ElvisTang123/Sumo_Bot/CAD Files/angledMotHolder.SLDPRT

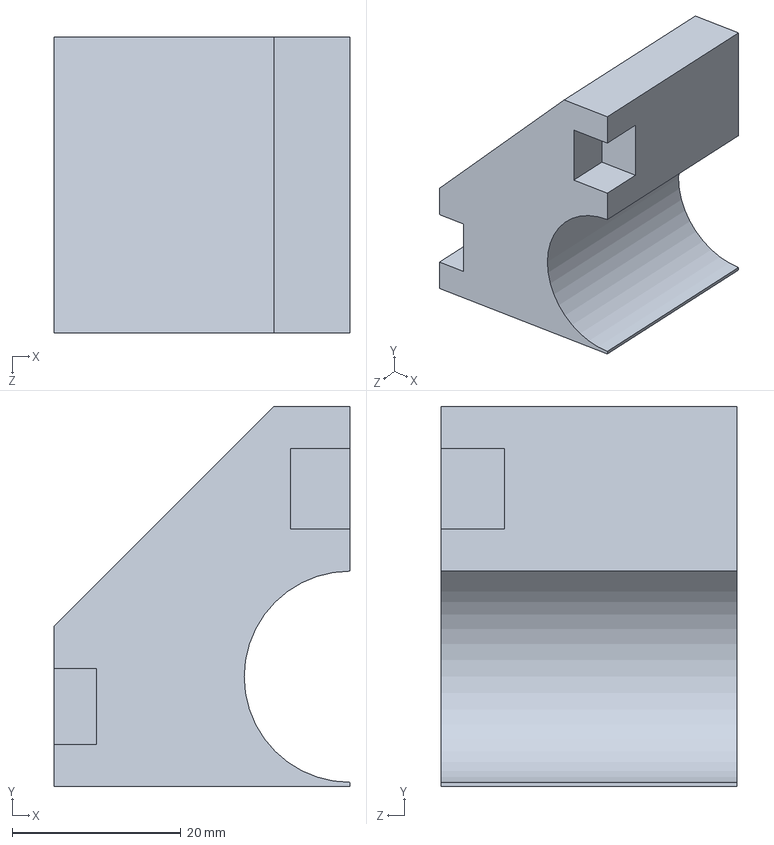
[picture p22: CAD file, 2022-08-17]
CAD Files/angledMotHolder.SLDPRT
35.0 x 45.0 x 35.0 mm
