ElvisTang123/Sumo_Bot/CAD Files/topplate.SLDPRT

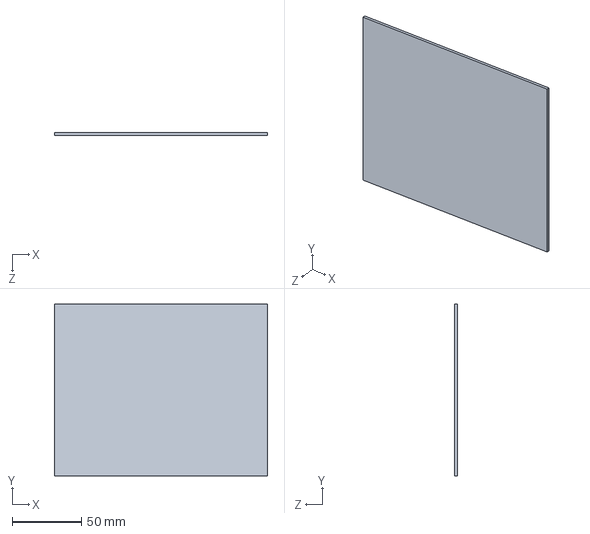
[picture p23: CAD file, 2022-08-17]
CAD Files/topplate.SLDPRT
154.0 x 124.0 x 2.00 mm
