ElvisTang123/Sumo_Bot/CAD Files/Hinge Rod.SLDPRT

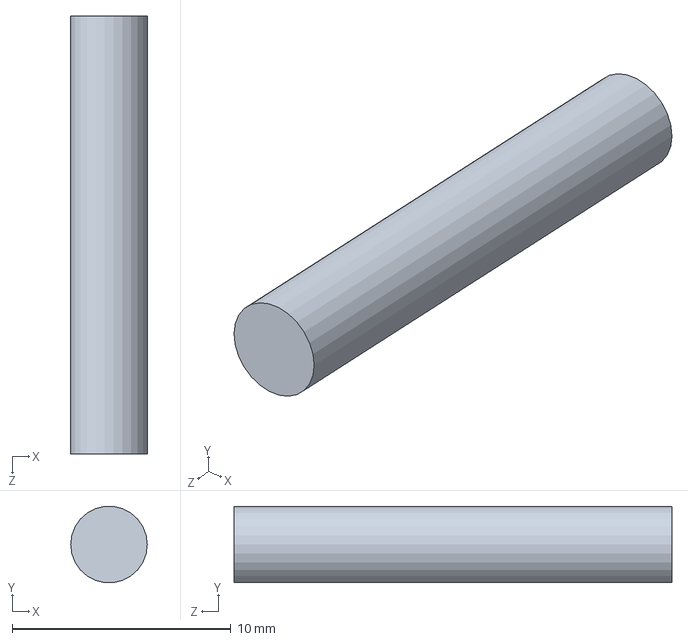
[picture p24: CAD file, 2022-08-17]
CAD Files/Hinge Rod.SLDPRT
3.50 x 3.47 x 20.0 mm
