ElvisTang123/Sumo_Bot/CAD Files/SMD Capacitor, MPU-9255.SLDPRT

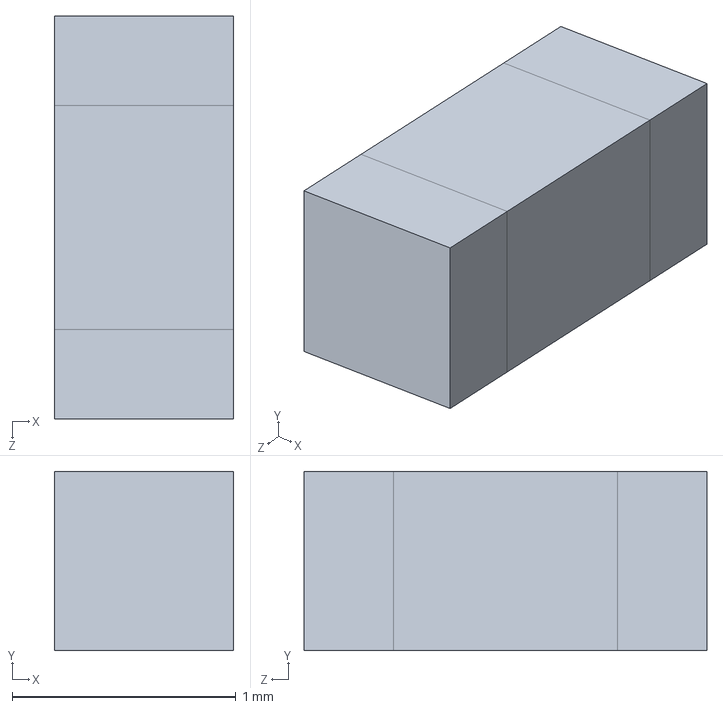
[picture p25: CAD file, 2022-08-17]
CAD Files/SMD Capacitor, MPU-9255.SLDPRT
0.8 x 0.8 x 1.80 mm
