ElvisTang123/Sumo_Bot/CAD Files/PCB, MPU-9255.SLDPRT

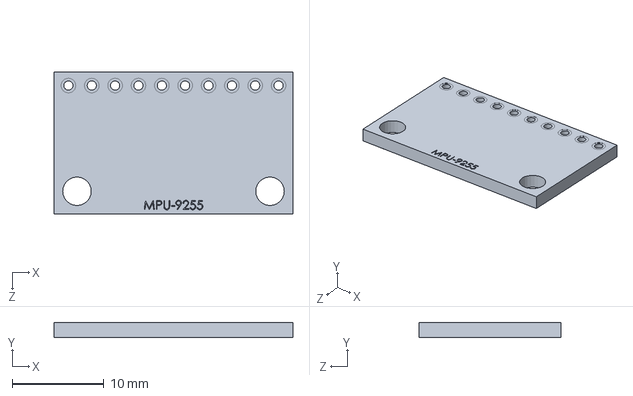
[picture p26: CAD file, 2022-08-17]
CAD Files/PCB, MPU-9255.SLDPRT
26.0 x 1.60 x 15.5 mm
