ElvisTang123/Sumo_Bot/CAD Files/SideWall.SLDPRT

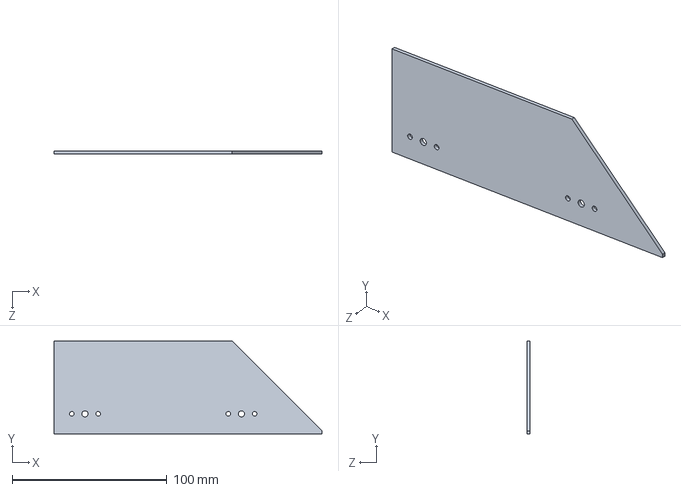
[picture p27: CAD file, 2022-08-17]
CAD Files/SideWall.SLDPRT
173.0 x 60.0 x 2.00 mm
