ElvisTang123/Sumo_Bot/CAD Files/SMD Resistor, 10kΩ, MPU-9255.SLDPRT

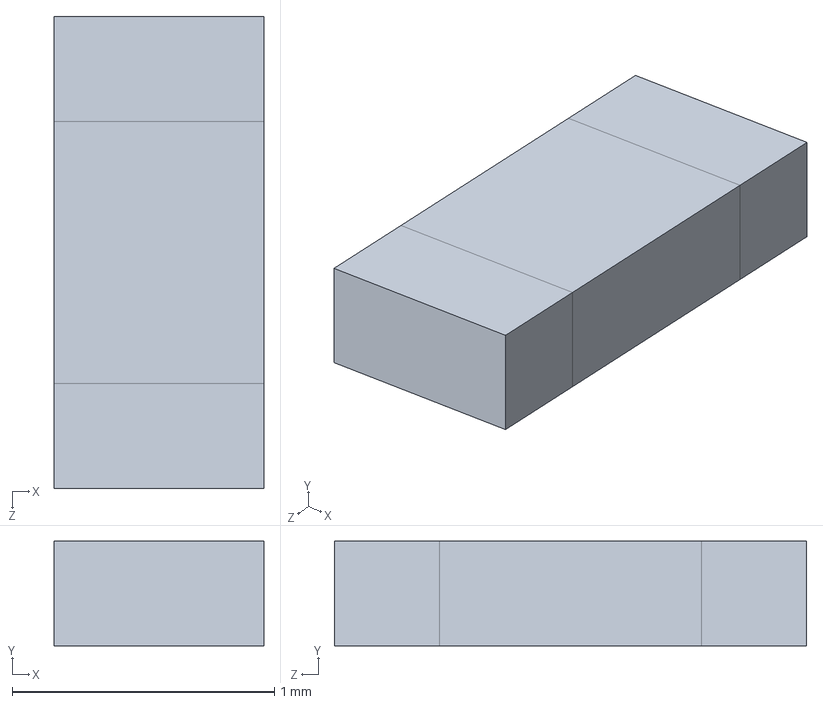
[picture p28: CAD file, 2022-08-17]
CAD Files/SMD Resistor, 10kΩ, MPU-9255.SLDPRT
0.8 x 0.4 x 1.80 mm
