ElvisTang123/Sumo_Bot/CAD Files/backplate.SLDPRT

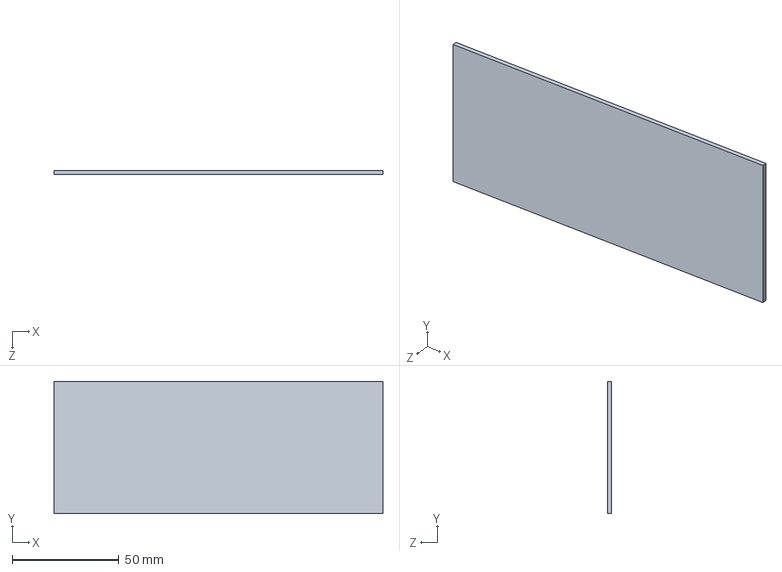
[picture p29: CAD file, 2022-08-17]
CAD Files/backplate.SLDPRT
154.0 x 62.0 x 2.00 mm
