ElvisTang123/Sumo_Bot/CAD Files/reciever.SLDPRT

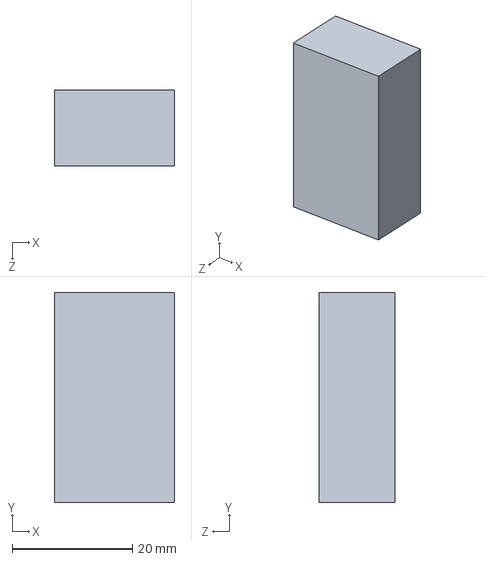
[picture p30: CAD file, 2022-08-17]
CAD Files/reciever.SLDPRT
20.0 x 35.0 x 12.7 mm
