ElvisTang123/Sumo_Bot/CAD Files/bot-angle.SLDPRT

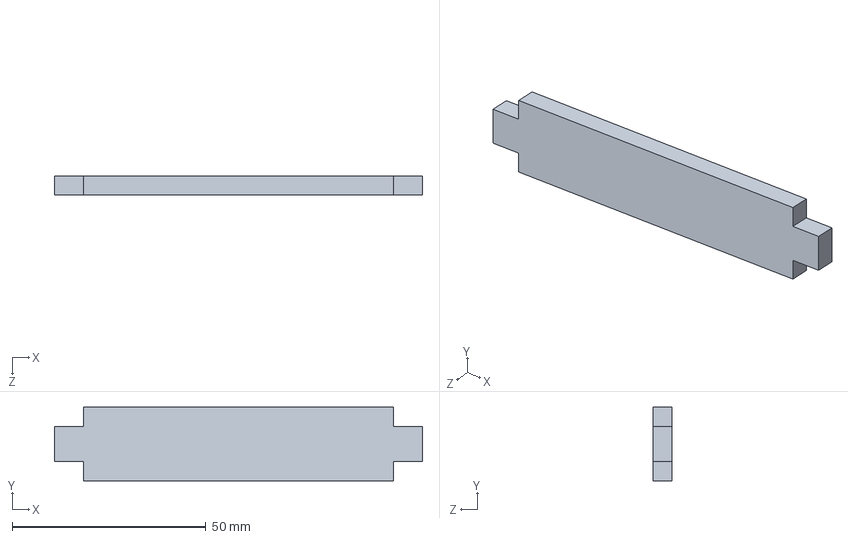
[picture p31: CAD file, 2022-08-17]
CAD Files/bot-angle.SLDPRT
95.0 x 19.0 x 5.00 mm
