ElvisTang123/Sumo_Bot/CAD Files/bottomPlate.SLDPRT

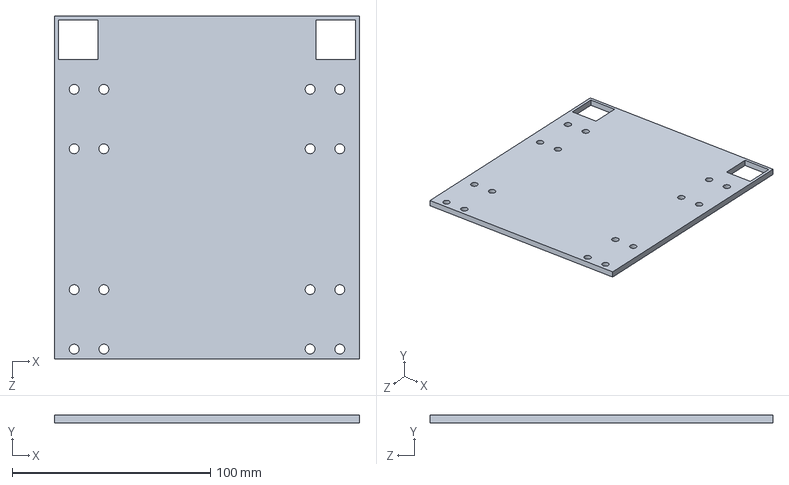
[picture p32: CAD file, 2022-08-17]
CAD Files/bottomPlate.SLDPRT
154.0 x 4.00 x 173.0 mm
