ElvisTang123/Sumo_Bot/CAD Files/vl53l0x_PCB.SLDPRT

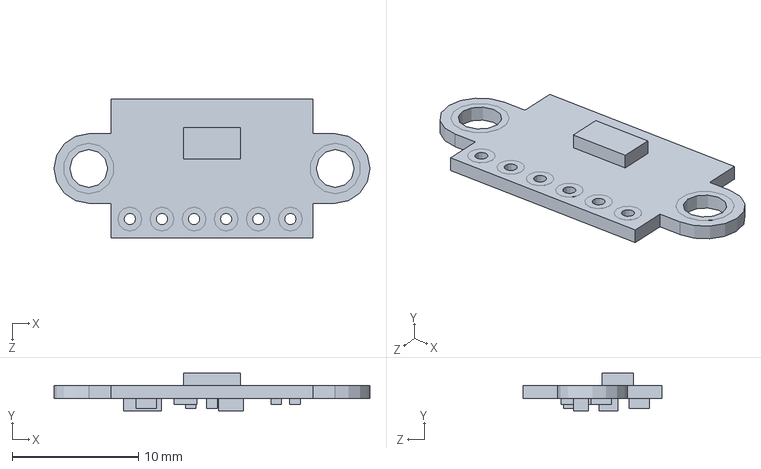
[picture p33: CAD file, 2022-08-17]
CAD Files/vl53l0x_PCB.SLDPRT
25.0 x 3.00 x 11.0 mm
