ElvisTang123/Sumo_Bot/CAD Files/Hinge2.SLDPRT

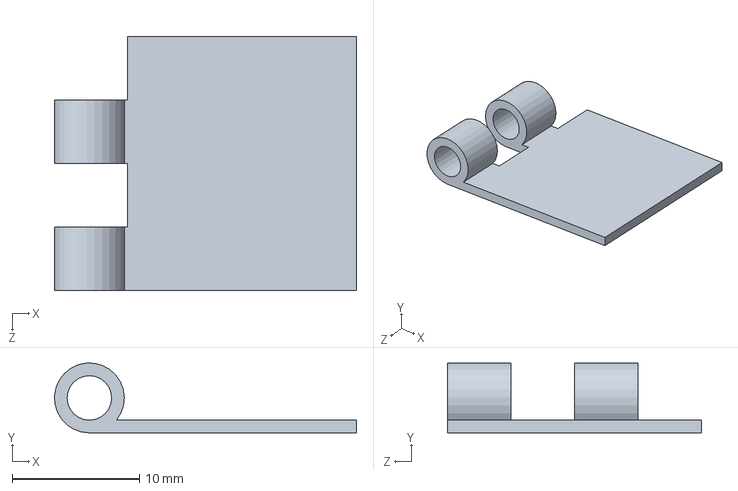
[picture p34: CAD file, 2022-08-17]
CAD Files/Hinge2.SLDPRT
23.7 x 5.49 x 20.0 mm
