ElvisTang123/Sumo_Bot/CAD Files/HC-SR04 Ultrasonic sensor.SLDPRT

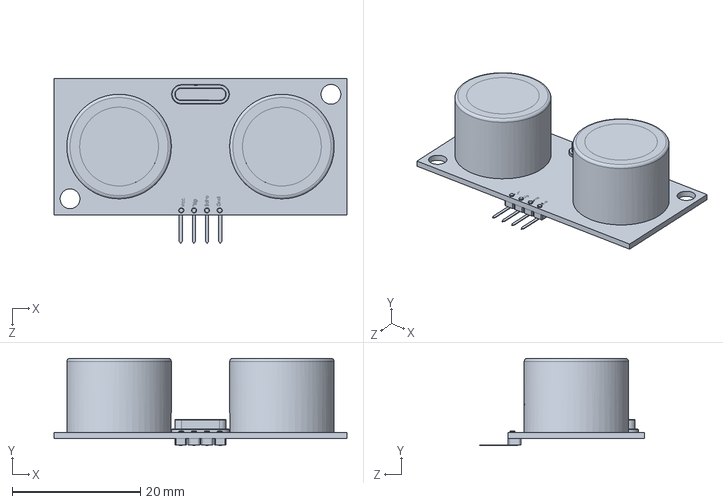
[picture p35: CAD file, 2022-08-17]
CAD Files/HC-SR04 Ultrasonic sensor.SLDPRT
45.7 x 13.6 x 25.8 mm
