ElvisTang123/Sumo_Bot/CAD Files/hinge1.SLDPRT

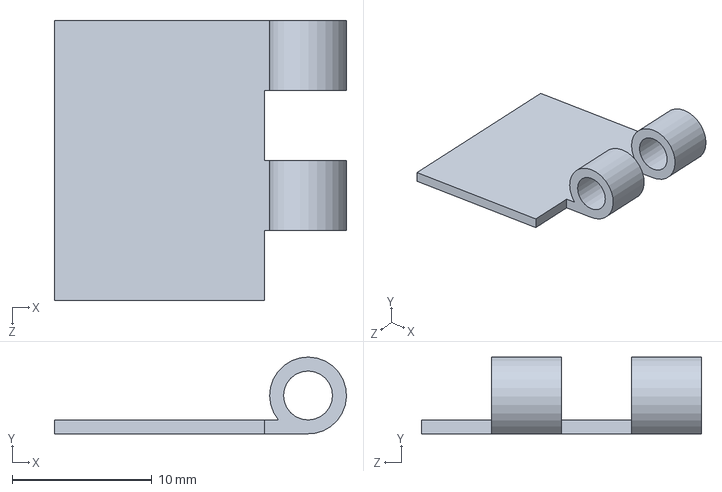
[picture p36: CAD file, 2022-08-17]
CAD Files/hinge1.SLDPRT
20.9 x 5.50 x 20.0 mm
