ElvisTang123/Sumo_Bot/CAD Files/motHolder.SLDPRT

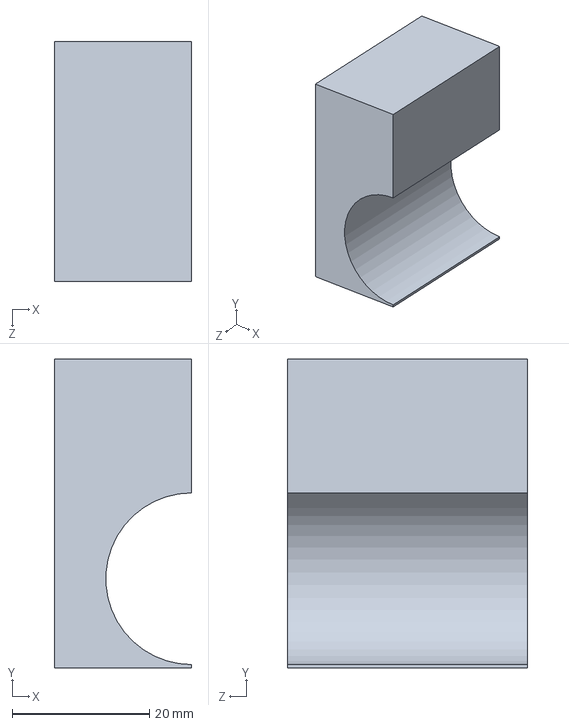
[picture p37: CAD file, 2022-08-17]
CAD Files/motHolder.SLDPRT
20.0 x 45.0 x 35.0 mm
