ElvisTang123/Sumo_Bot/CAD Files/pin_header.SLDPRT

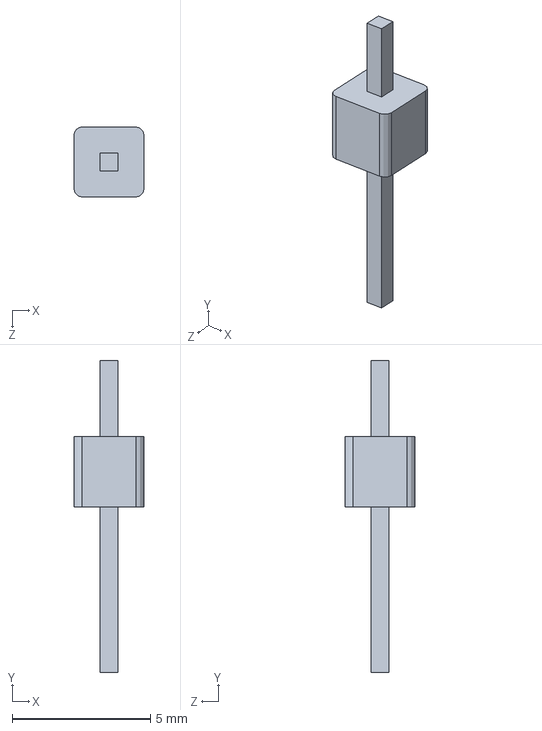
[picture p38: CAD file, 2022-08-17]
CAD Files/pin_header.SLDPRT
2.54 x 11.3 x 2.54 mm
