ElvisTang123/Sumo_Bot/Program Files/Core/Src/Motor_Driver.c

/*
 * Motor_Driver.c
 *
 *  Created on: Aug 8, 2022
 *      Author: Prestige
 */

#include "motor_driver.h"

void enable(Motor_t* mot)
{
	HAL_GPIO_WritePin(mot->EN_GPIO, mot->EN_pin, GPIO_PIN_SET);

}

void disable(Motor_t* mot)
{
	HAL_GPIO_WritePin(mot->EN_GPIO, mot->EN_pin, GPIO_PIN_RESET);
}

void set_level(Motor_t* mot, int32_t level)
{
	if(level>=0){
		__HAL_TIM_SET_COMPARE(mot->htim ,mot->IN1_pin, level);
		__HAL_TIM_SET_COMPARE(mot->htim ,mot->IN2_pin, 0);
	}
	else{
		__HAL_TIM_SET_COMPARE(mot->htim ,mot->IN1_pin, 0);
		__HAL_TIM_SET_COMPARE(mot->htim ,mot->IN2_pin, -(level));
	}
}
